angmolin/ChessPieceScanner/doc/Resources/Images/Chess pieces/muestra1.jpg

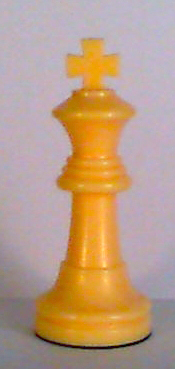
doc/Resources/Images/Chess pieces/muestra1.jpg
