angmolin/ChessPieceScanner/3d pieces/png/BoardSeparator.PNG

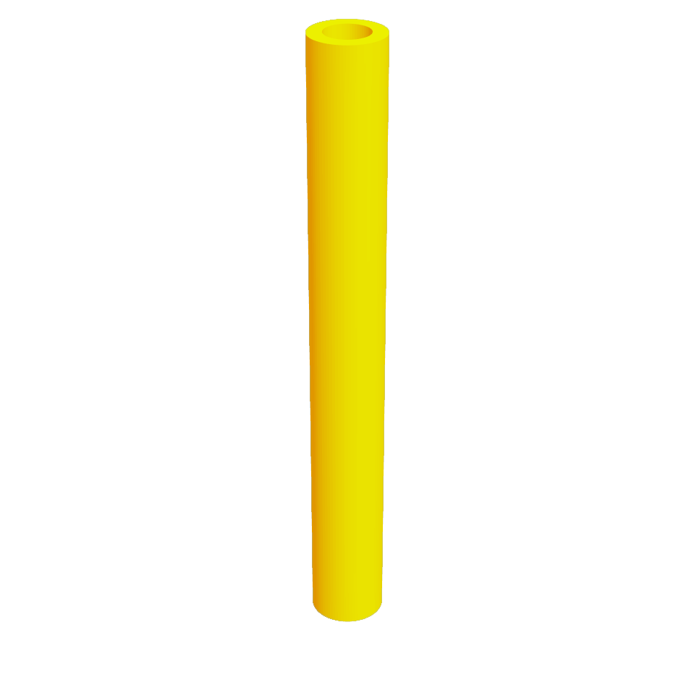
3d pieces/png/BoardSeparator.PNG
