angmolin/ChessPieceScanner/3d pieces/png/CableGrommet.PNG

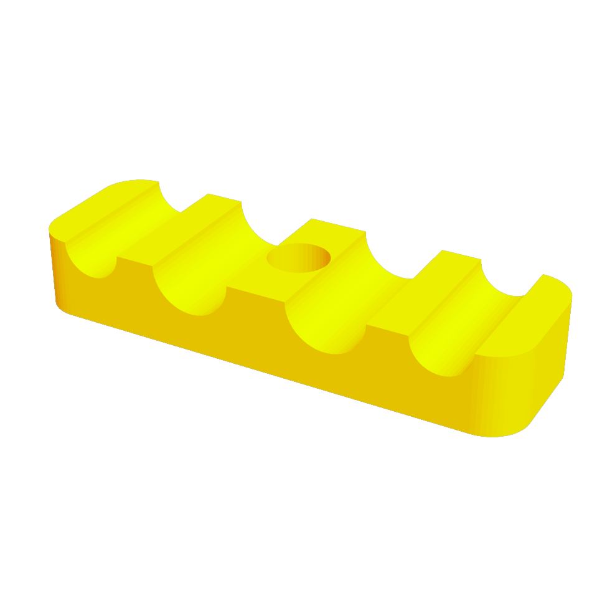
3d pieces/png/CableGrommet.PNG
