angmolin/ChessPieceScanner/3d pieces/png/CameraBackCover.PNG

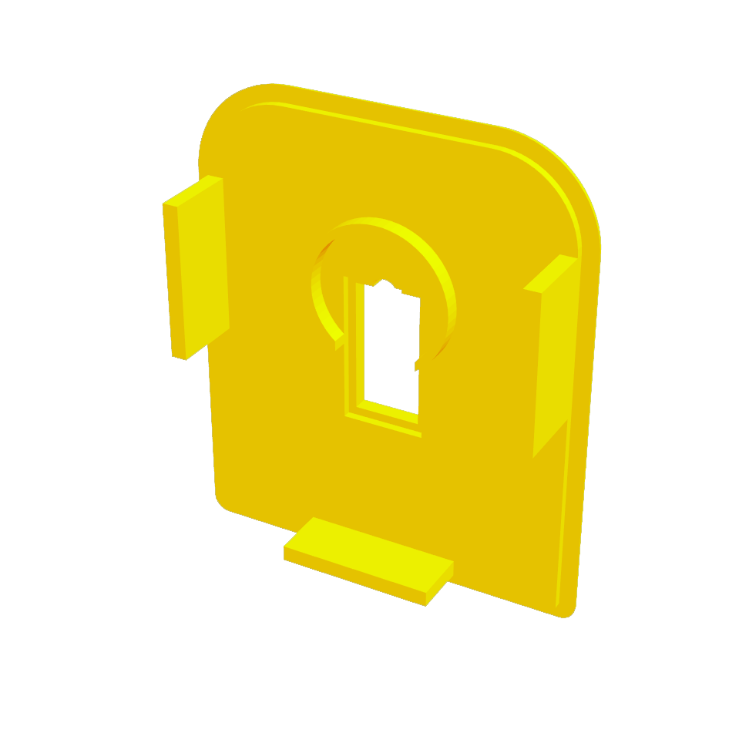
3d pieces/png/CameraBackCover.PNG
