angmolin/ChessPieceScanner/3d pieces/png/CameraBox.PNG

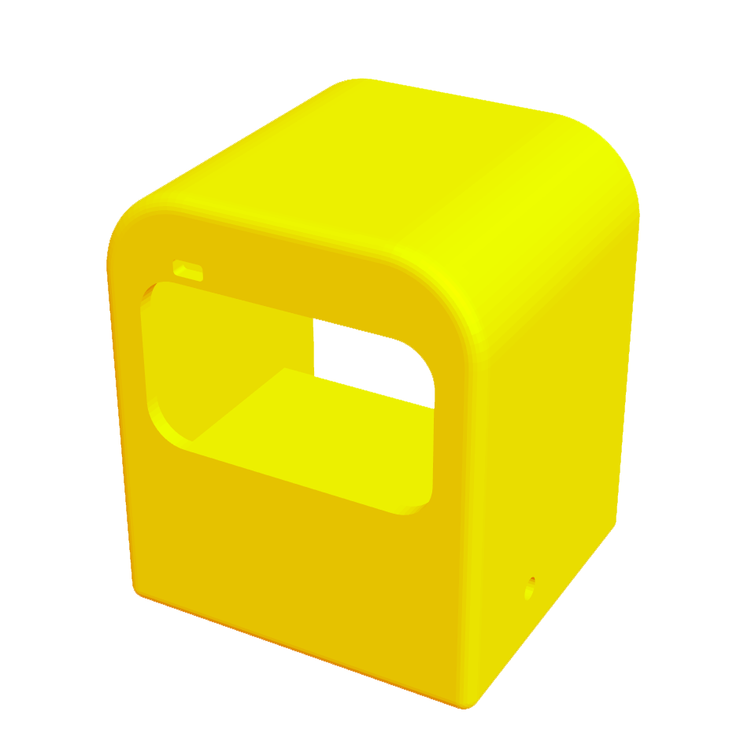
3d pieces/png/CameraBox.PNG
