angmolin/ChessPieceScanner/3d pieces/png/CameraCableCover.PNG

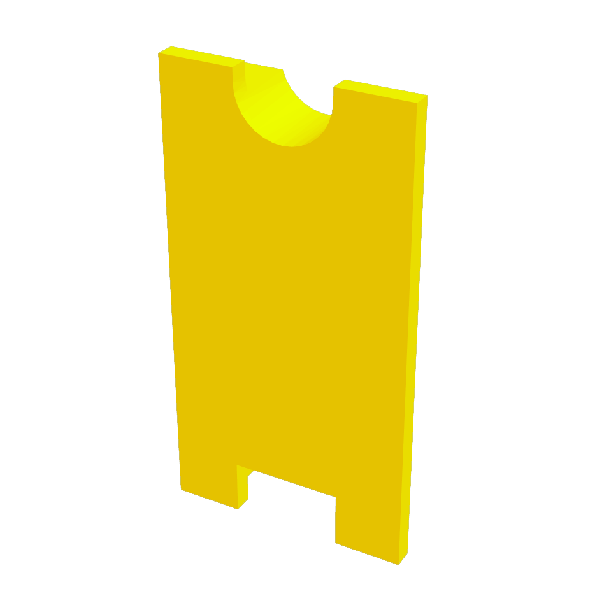
3d pieces/png/CameraCableCover.PNG
