angmolin/ChessPieceScanner/3d pieces/png/CameraSupport.PNG

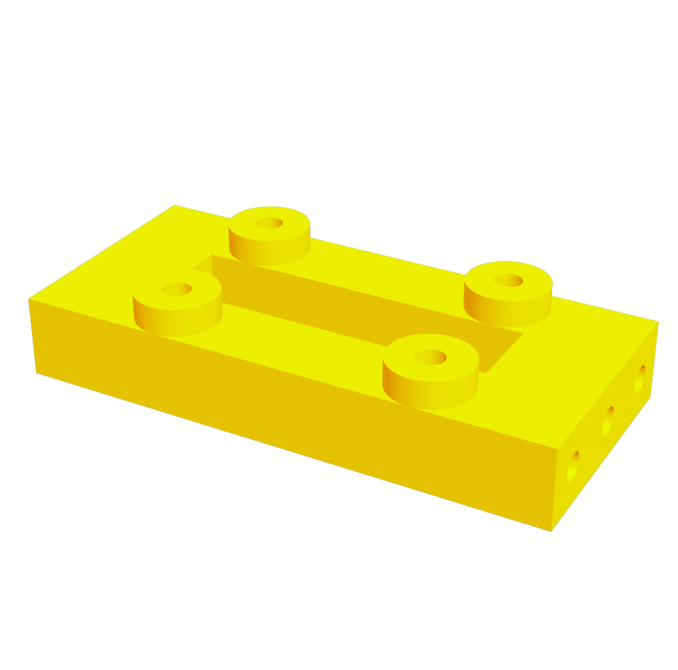
3d pieces/png/CameraSupport.PNG
