angmolin/ChessPieceScanner/3d pieces/png/DownRightCurtainSupport.PNG

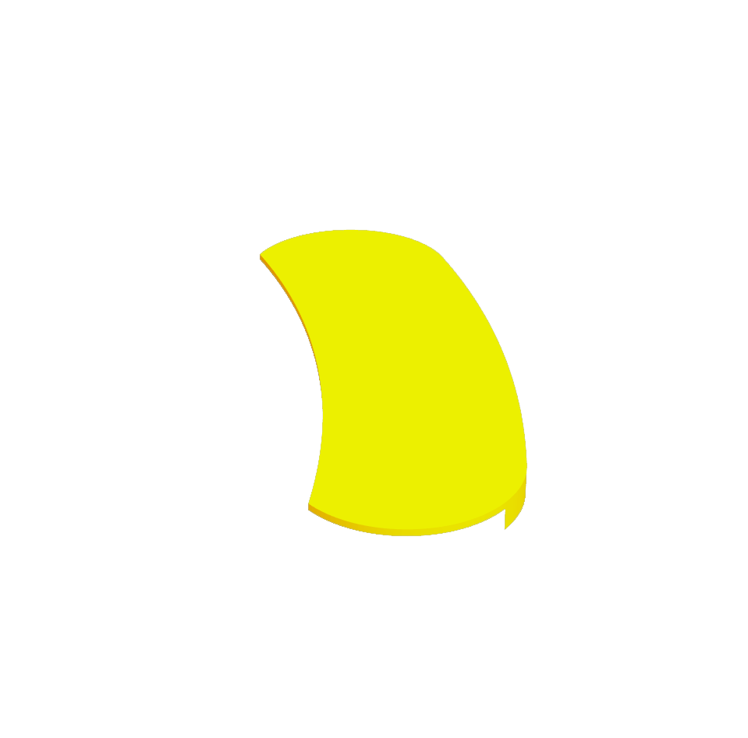
3d pieces/png/DownRightCurtainSupport.PNG
