angmolin/ChessPieceScanner/3d pieces/png/LegSeparator.PNG

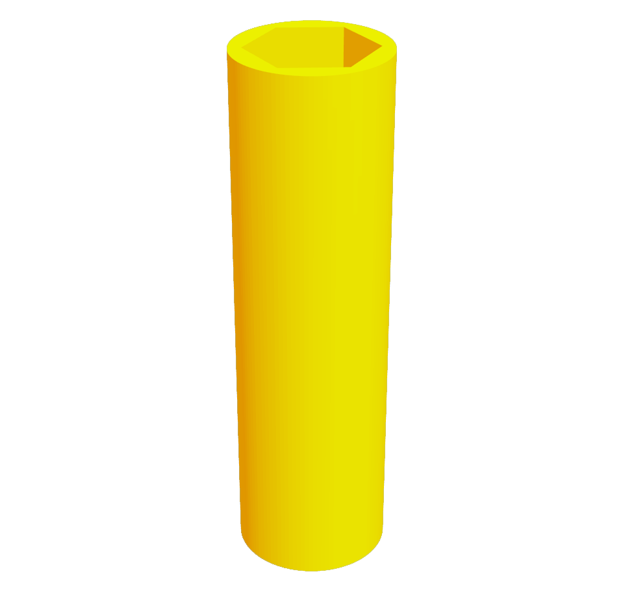
3d pieces/png/LegSeparator.PNG
