angmolin/ChessPieceScanner/3d pieces/png/TopBaseFixer.PNG

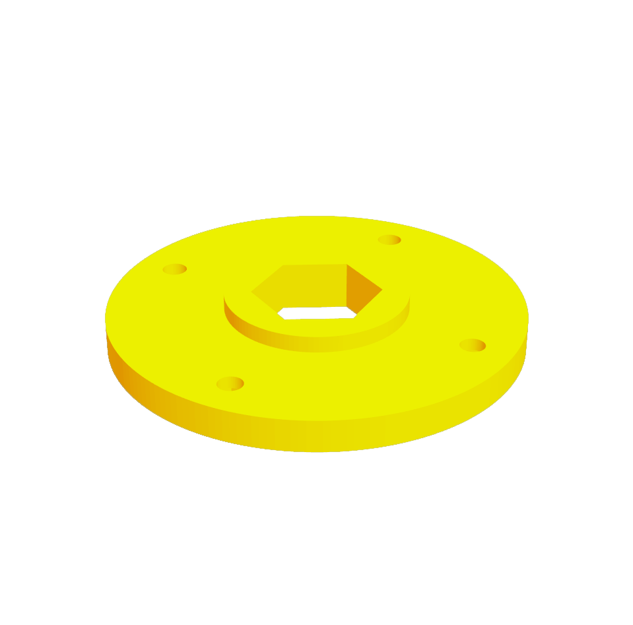
3d pieces/png/TopBaseFixer.PNG
