angmolin/ChessPieceScanner/3d pieces/png/UpLeftCurtainSupport.PNG

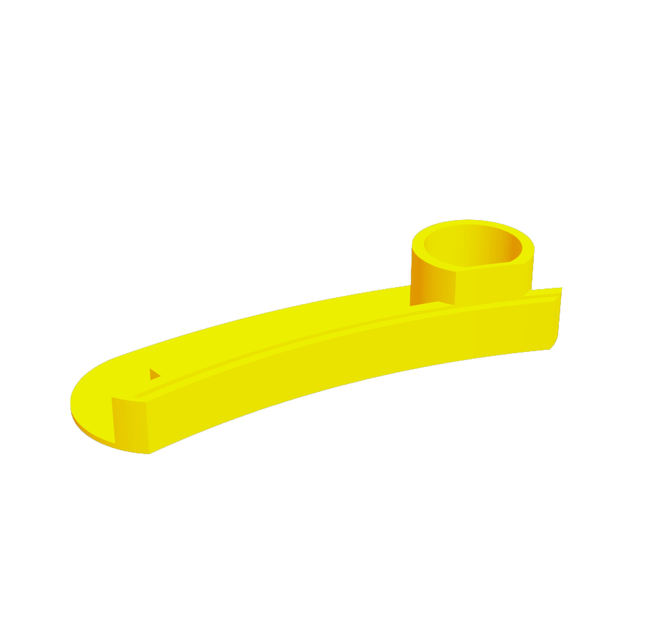
3d pieces/png/UpLeftCurtainSupport.PNG
