angmolin/ChessPieceScanner/3d pieces/png/UpRightCurtainSupport.PNG

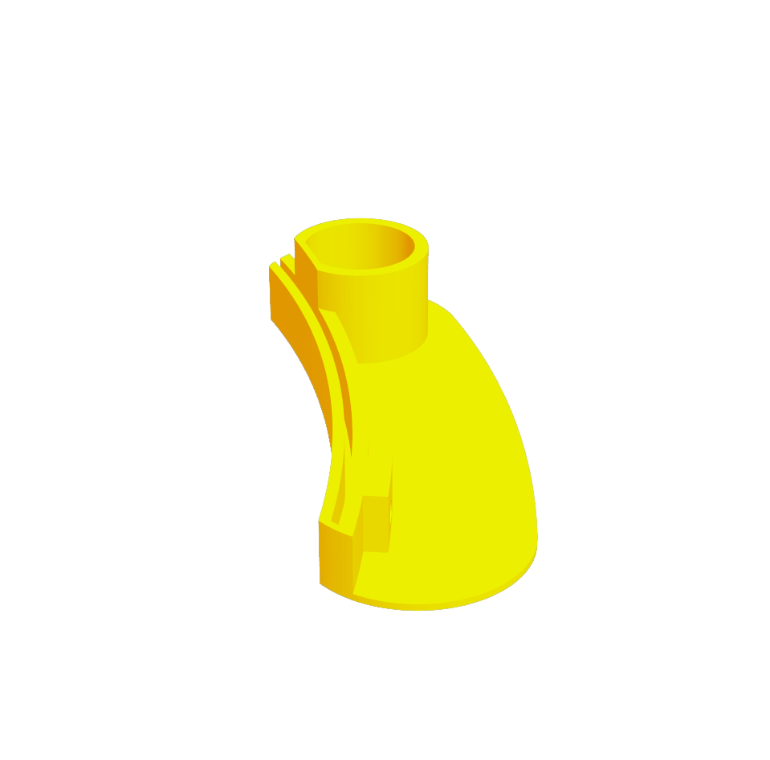
3d pieces/png/UpRightCurtainSupport.PNG
