angmolin/ChessPieceScanner/3d pieces/png/YAxisBearingSupport.PNG

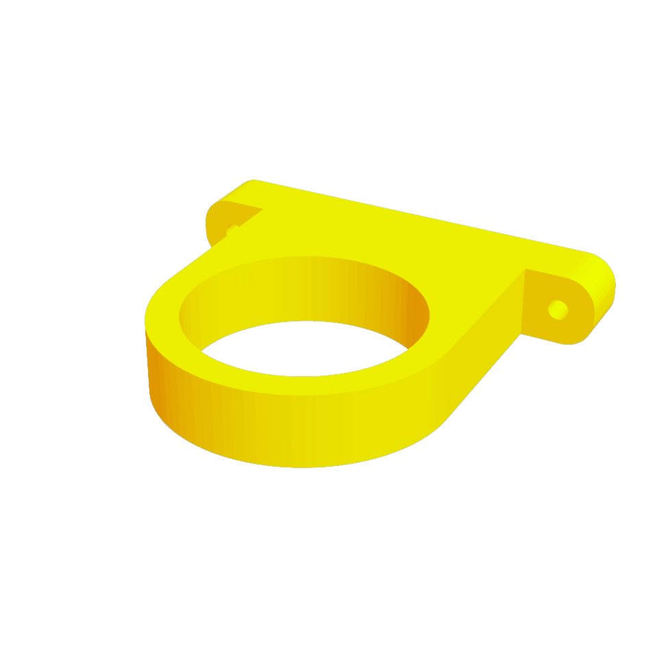
3d pieces/png/YAxisBearingSupport.PNG
