angmolin/ChessPieceScanner/3d pieces/png/YAxisBearingSupportSeparator.PNG

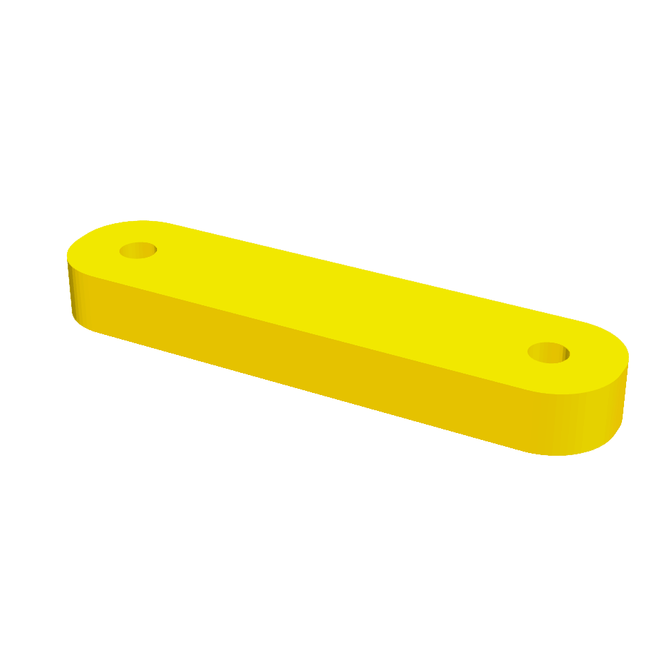
3d pieces/png/YAxisBearingSupportSeparator.PNG
