angmolin/ChessPieceScanner/3d pieces/png/YAxisLimitSwitchSupport.PNG

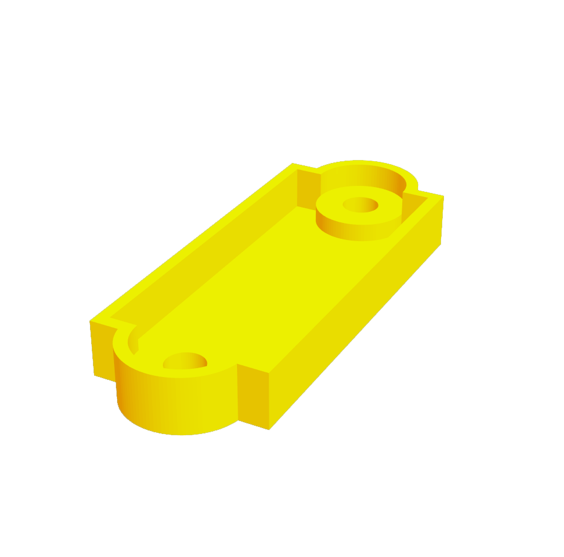
3d pieces/png/YAxisLimitSwitchSupport.PNG
