angmolin/ChessPieceScanner/3d pieces/png/YAxisMotorSupport.PNG

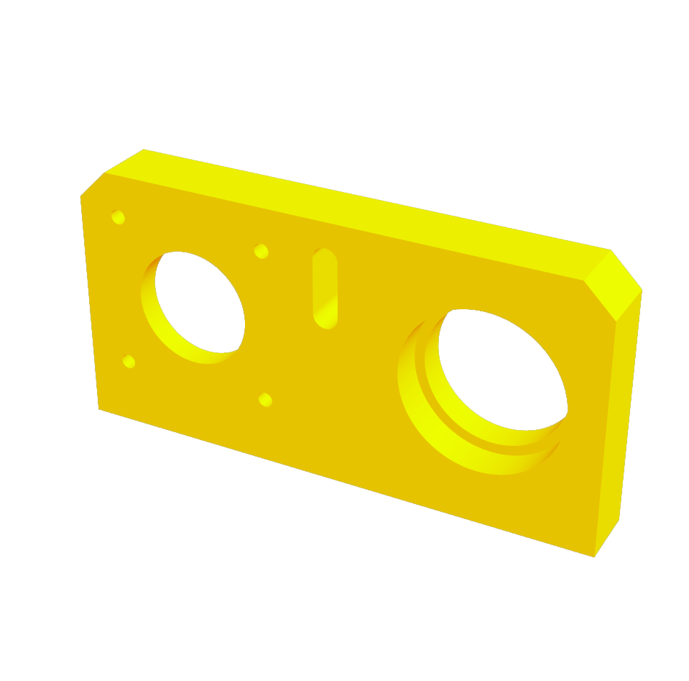
3d pieces/png/YAxisMotorSupport.PNG
