angmolin/ChessPieceScanner/3d pieces/png/YAxisTachometer.PNG

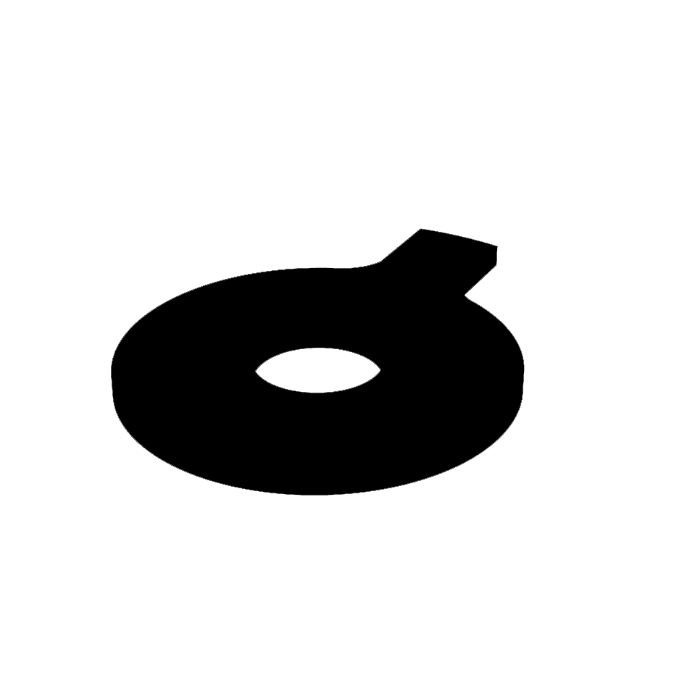
3d pieces/png/YAxisTachometer.PNG
