angmolin/ChessPieceScanner/3d pieces/png/ZAxisLimitSwitchCover.PNG

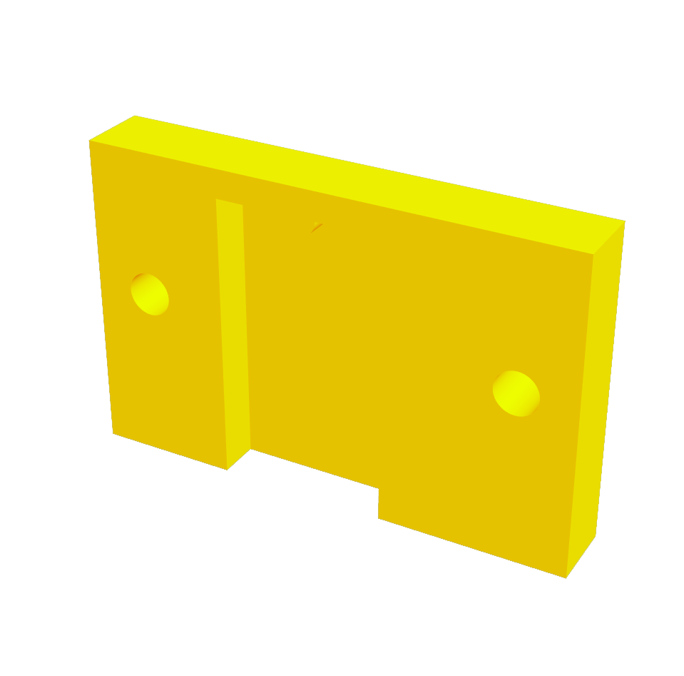
3d pieces/png/ZAxisLimitSwitchCover.PNG
