angmolin/ChessPieceScanner/doc/Resources/Images/Chess pieces/muestra3.jpg

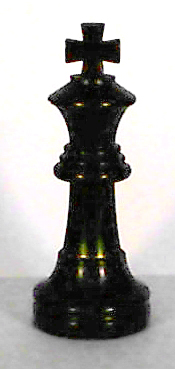
doc/Resources/Images/Chess pieces/muestra3.jpg
