angmolin/ChessPieceScanner/doc/Resources/Images/Chess pieces/muestra4.jpg

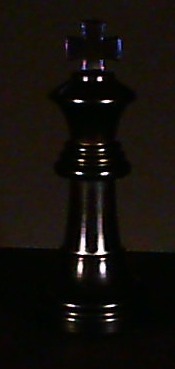
doc/Resources/Images/Chess pieces/muestra4.jpg
