angmolin/ChessPieceScanner/doc/Resources/Images/Terminal/Asistente1.png

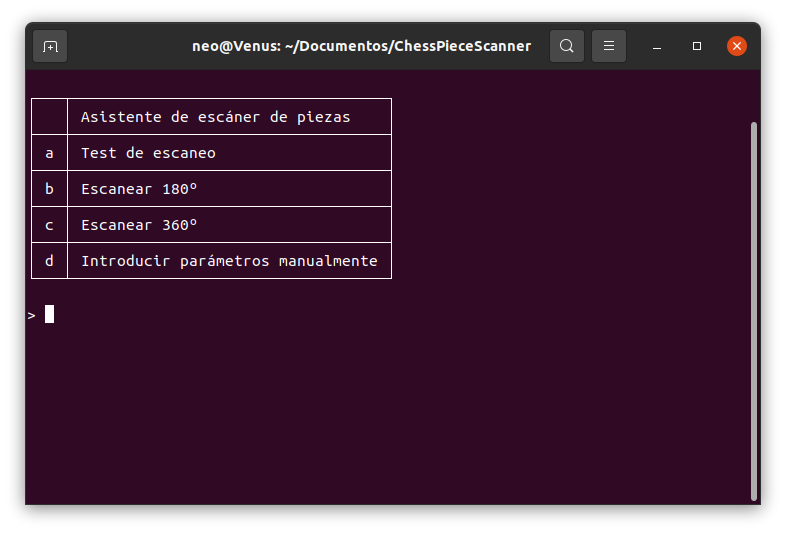
doc/Resources/Images/Terminal/Asistente1.png
