angmolin/ChessPieceScanner/photos/EMPTY_B/empty1.jpg

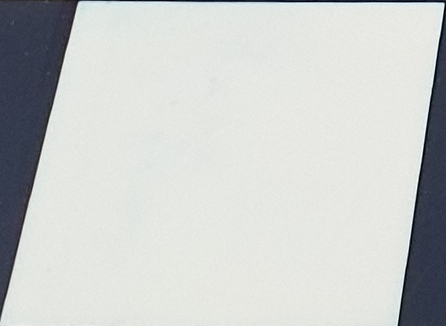
photos/EMPTY_B/empty1.jpg
