angmolin/ChessPieceScanner/photos/EMPTY_B/empty2.jpg

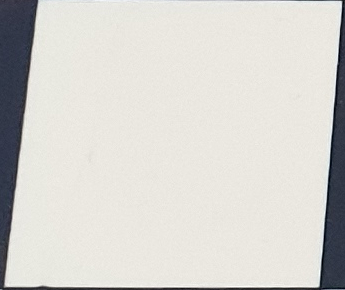
photos/EMPTY_B/empty2.jpg
