angmolin/ChessPieceScanner/photos/EMPTY_B/empty3.jpg

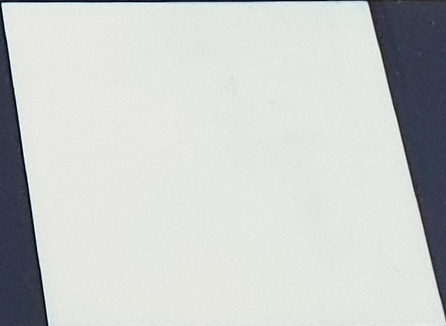
photos/EMPTY_B/empty3.jpg
