angmolin/ChessPieceScanner/photos/EMPTY_B/empty4.jpg

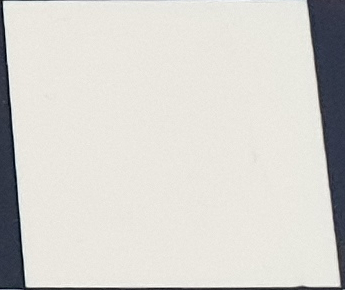
photos/EMPTY_B/empty4.jpg
