angmolin/ChessPieceScanner/photos/EMPTY_N/empty1.jpg

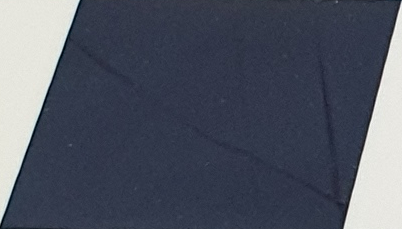
photos/EMPTY_N/empty1.jpg
