angmolin/ChessPieceScanner/photos/EMPTY_N/empty2.jpg

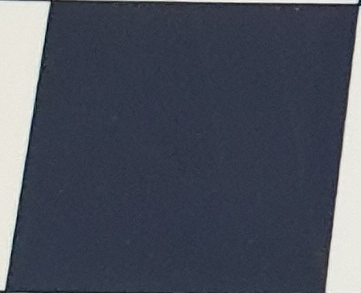
photos/EMPTY_N/empty2.jpg
