angmolin/ChessPieceScanner/photos/EMPTY_N/empty3.jpg

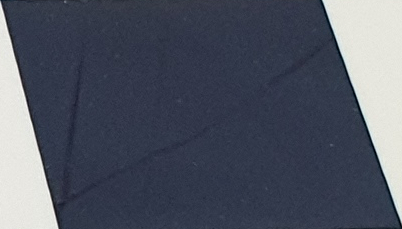
photos/EMPTY_N/empty3.jpg
