angmolin/ChessPieceScanner/photos/EMPTY_N/empty4.jpg

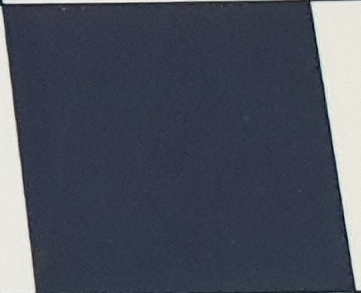
photos/EMPTY_N/empty4.jpg
