angmolin/ChessPieceScanner/3d pieces/stl/RightCameraSupport.stl

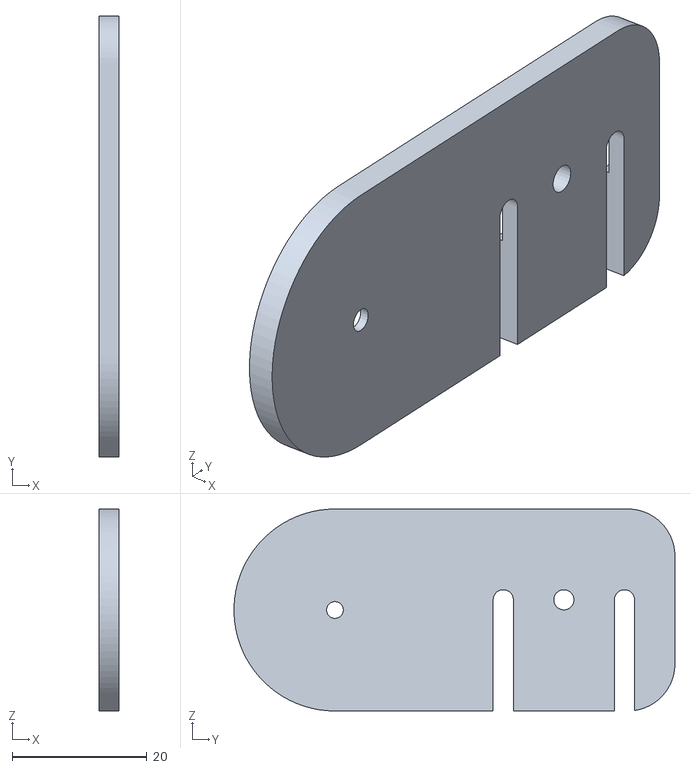
[picture p62: CAD file, 2021-05-11]
3d pieces/stl/RightCameraSupport.stl
3.00 x 65.5 x 30.0
