angmolin/ChessPieceScanner/3d pieces/stl/BoardSeparator.stl

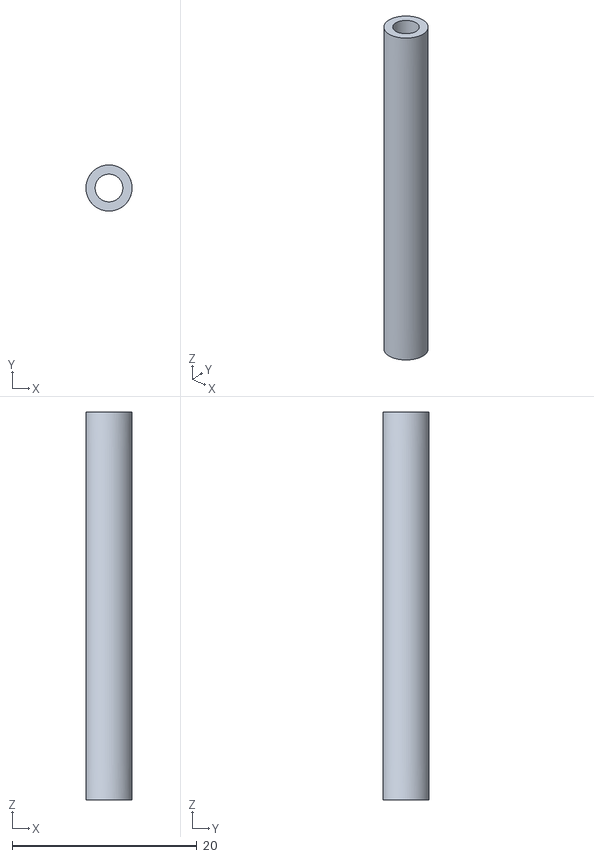
[picture p63: CAD file, 2021-05-11]
3d pieces/stl/BoardSeparator.stl
5.00 x 5.00 x 42.0
