angmolin/ChessPieceScanner/3d pieces/stl/CableGrommet.stl

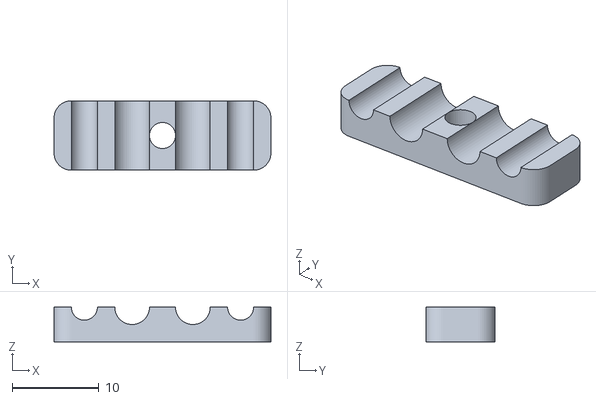
[picture p64: CAD file, 2021-05-11]
3d pieces/stl/CableGrommet.stl
25.0 x 8.00 x 4.00
