angmolin/ChessPieceScanner/3d pieces/stl/UpRightCurtainSupport.stl

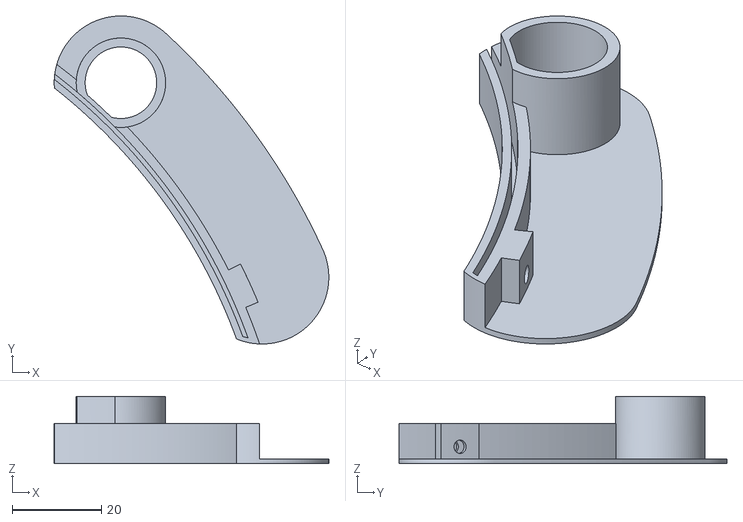
[picture p65: CAD file, 2021-05-11]
3d pieces/stl/UpRightCurtainSupport.stl
61.4 x 73.4 x 15.0
