angmolin/ChessPieceScanner/3d pieces/stl/CameraCableCover.stl

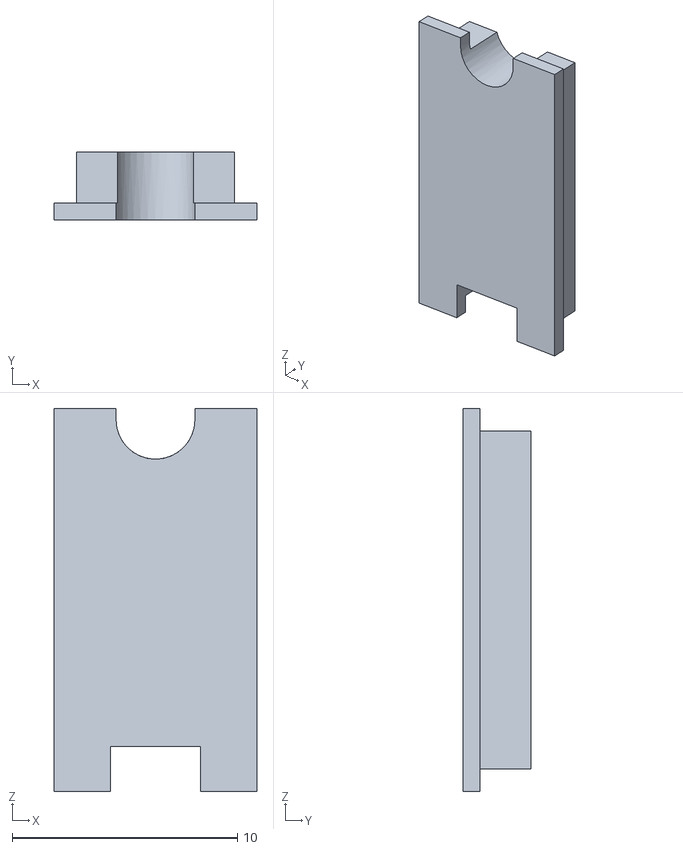
[picture p66: CAD file, 2021-05-11]
3d pieces/stl/CameraCableCover.stl
9.00 x 3.00 x 17.0
