angmolin/ChessPieceScanner/3d pieces/stl/ZAxisMotorSupport.stl

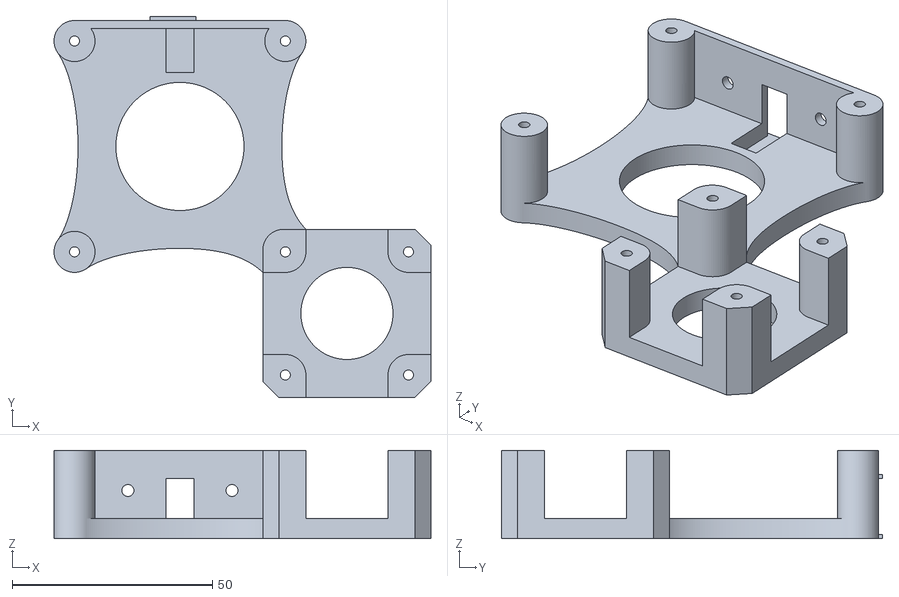
[picture p67: CAD file, 2021-05-11]
3d pieces/stl/ZAxisMotorSupport.stl
94.2 x 95.2 x 22.0
