angmolin/ChessPieceScanner/3d pieces/stl/YAxisMotorBackSupport.stl

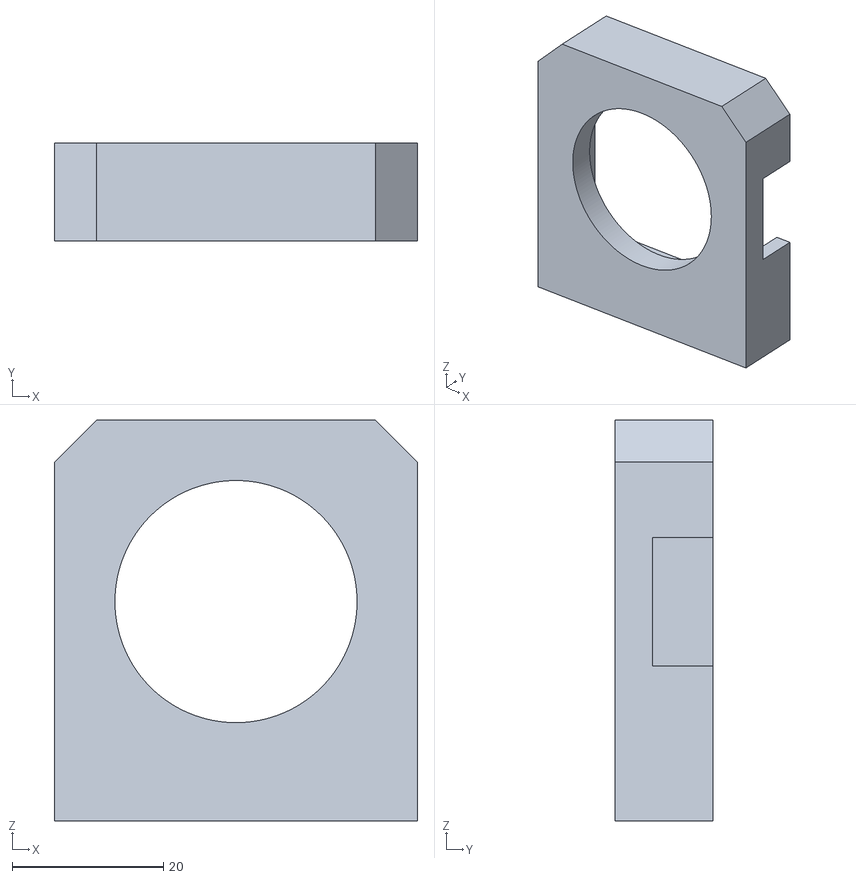
[picture p68: CAD file, 2021-05-11]
3d pieces/stl/YAxisMotorBackSupport.stl
48.0 x 13.0 x 53.0
