angmolin/ChessPieceScanner/3d pieces/stl/LegSeparator.stl

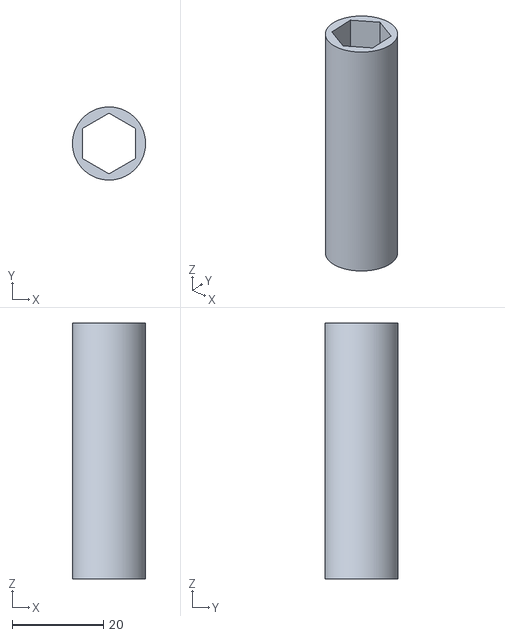
[picture p69: CAD file, 2021-05-11]
3d pieces/stl/LegSeparator.stl
16.0 x 16.0 x 56.0
