angmolin/ChessPieceScanner/doc/Resources/Images/Terminal/Manual.png

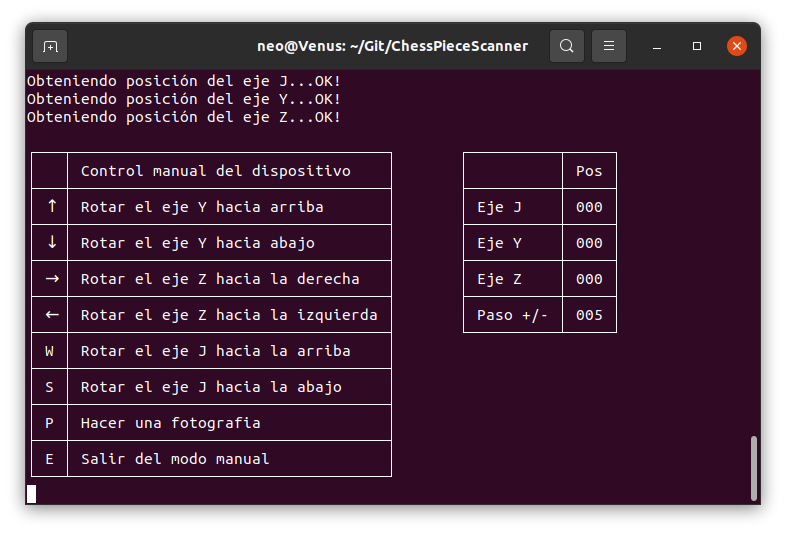
doc/Resources/Images/Terminal/Manual.png
